csemaan10/Carleton-EmergencyTrackingGPS/designs/Software/Backend/AuthenticationProviderExample.png

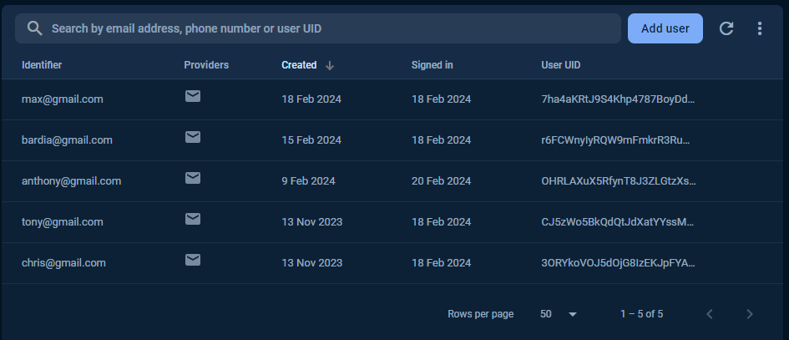
designs/Software/Backend/AuthenticationProviderExample.png
