csemaan10/Carleton-EmergencyTrackingGPS/designs/Software/Backend/CoordinatesCollectionExample.png

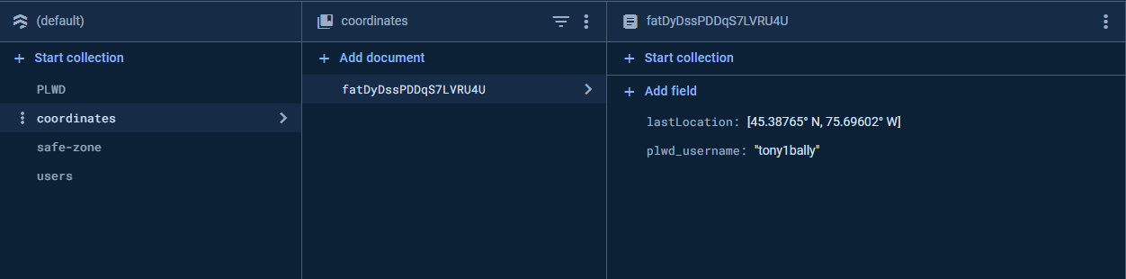
designs/Software/Backend/CoordinatesCollectionExample.png
