csemaan10/Carleton-EmergencyTrackingGPS/designs/Software/Pages/settings.png

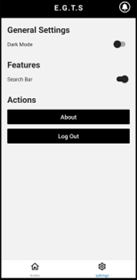
designs/Software/Pages/settings.png
